fan-ziqi/My_HoloCubic/2.Firmware/HoloCubic-new/FirmwareCode/src/imu.h

#ifndef IMU_H
#define IMU_H


#include <I2Cdev.h>
#include <MPU6050.h>
#include "lv_port_indev.h"

#define IMU_I2C_SDA 32 
#define IMU_I2C_SCL 33


extern int32_t encoder_diff;
extern lv_indev_state_t encoder_state;
extern boolean image_flag;


enum ACTIVE_TYPE
{
      TURN_RIGHT = 0, TURN_LEFT, RETURN, GO_FORWORD, UNKNOWN
};

struct Imu_Active
{
	boolean  isValid;
	ACTIVE_TYPE active;
	boolean long_time;
	int16_t ax;
	int16_t ay;
	int16_t az;
	int16_t gx;
	int16_t gy;
	int16_t gz;
};

class IMU
{
private:
	MPU6050 imu;
	int flag;
	long  last_update_time;

	int16_t ax, ay, az;
	int16_t gx, gy, gz;

public:
	Imu_Active active_info;
	void init();
	Imu_Active* update(int interval);

};

#endif
