fan-ziqi/My_HoloCubic/2.Firmware/HoloCubic-new/FirmwareCode/src/lv_cubic_gui.c

/*********************
        INCLUDES
 *********************/
#include "lv_cubic_gui.h"
#include "images.h"

// 必须定义为全局或者静态
lv_obj_t *scr[4];

lv_obj_t *weather_image;
lv_obj_t *cityname_label;
lv_obj_t *temperature_label;
lv_obj_t *C_label;

lv_obj_t *time_image;
lv_obj_t *date_label;
lv_obj_t *time_label;

lv_obj_t *cpu_temp_label;
lv_obj_t *cpu_used_label;
lv_obj_t *mem_used_label;
lv_obj_t *net_upload_label;
lv_obj_t *net_download_label;

lv_obj_t *photo_image;

lv_font_declare(lv_font_montserrat_20);
lv_font_declare(lv_font_montserrat_24);
lv_font_declare(lv_font_montserrat_40);

// 天气图标路径的映射关系
void *image_map[] = {&Sunny, &Clear, "S:/Weather/2.bin", "S:/Weather/3.bin",
                     &Cloudy, &PartlyCloudy, &Overcast, &ModerateSnow,
                     &Thundershower, "S:/Weather/12.bin", &LightRain,
                     &ModerateRain, &HeavyRain, "S:/Weather/19.bin",
                     &Sleet, &SnowFlurry, &LightSnow, &HeavySnow,
                     "S:/Weather/26.bin", "S:/Weather/27.bin", "S:/Weather/28.bin",
                     "S:/Weather/29.bin", "S:/Weather/30.bin", "S:/Weather/31.bin",
                     "S:/Weather/32.bin", "S:/Weather/33.bin", "S:/Weather/34.bin",
                     "S:/Weather/35.bin", "S:/Weather/36.bin", "S:/Weather/37.bin",
                     "S:/Weather/38.bin", "S:/Weather/99.bin"};
int map_index[] = {0, 1, 2, 3, 4, 5, 5, 5, 5, 6,
                   7, 8, 9, 10, 11, 12, 12, 12, 12, 13,
                   14, 15, 16, 7, 17, 17, 18, 19, 20, 21,
                   22, 23, 24, 25, 26, 27, 28, 29, 30};

// static lv_group_t *g;
// static lv_obj_t *tv;
// static lv_obj_t *t1;
// static lv_obj_t *t2;
// static lv_obj_t *t3;
static lv_style_t default_style;
static lv_style_t label_style1;
static lv_style_t label_style3;
static lv_style_t label_style4;
static lv_style_t label_style5;

void display_init(void)
{
  lv_style_init(&default_style);
  lv_style_set_bg_color(&default_style, LV_STATE_DEFAULT, LV_COLOR_BLACK);
  lv_style_set_bg_color(&default_style, LV_STATE_PRESSED, LV_COLOR_GRAY);
  lv_style_set_bg_color(&default_style, LV_STATE_FOCUSED, LV_COLOR_BLACK);
  lv_style_set_bg_color(&default_style, LV_STATE_FOCUSED | LV_STATE_PRESSED, lv_color_hex(0xf88));
  lv_obj_add_style(lv_scr_act(), LV_BTN_PART_MAIN, &default_style);

  // scr[0] = lv_scr_act(); //在第一页创建
  // 天气页初始化
  scr[0] = lv_obj_create(NULL, NULL);
  lv_obj_add_style(scr[0], LV_BTN_PART_MAIN, &default_style);
  lv_style_init(&label_style1);
  lv_style_set_text_opa(&label_style1, LV_STATE_DEFAULT, LV_OPA_COVER);
  lv_style_set_text_color(&label_style1, LV_STATE_DEFAULT, LV_COLOR_WHITE);
  lv_style_set_text_font(&label_style1, LV_STATE_DEFAULT, &lv_font_montserrat_24);
  lv_style_init(&label_style3);
  lv_style_set_text_opa(&label_style3, LV_STATE_DEFAULT, LV_OPA_COVER);
  lv_style_set_text_color(&label_style3, LV_STATE_DEFAULT, LV_COLOR_WHITE);
  lv_style_set_text_font(&label_style3, LV_STATE_DEFAULT, &lv_font_montserrat_24);
  weather_image = lv_img_create(scr[0], NULL);
  cityname_label = lv_label_create(scr[0], NULL);
  temperature_label = lv_label_create(scr[0], NULL);
  C_label = lv_label_create(scr[0], NULL);

  // 日期时间页初始化
  scr[1] = lv_obj_create(NULL, NULL);
  lv_obj_add_style(scr[1], LV_BTN_PART_MAIN, &default_style);
  lv_style_init(&label_style5);
  lv_style_set_text_opa(&label_style5, LV_STATE_DEFAULT, LV_OPA_COVER);
  lv_style_set_text_color(&label_style5, LV_STATE_DEFAULT, LV_COLOR_WHITE);
  lv_style_set_text_font(&label_style5, LV_STATE_DEFAULT, &lv_font_montserrat_40);
  time_image = lv_img_create(scr[1], NULL);
  date_label = lv_label_create(scr[1], NULL);
  time_label = lv_label_create(scr[1], NULL);

  // 硬件信息页初始化
  scr[2] = lv_obj_create(NULL, NULL);
  lv_obj_add_style(scr[2], LV_BTN_PART_MAIN, &default_style);
  lv_style_init(&label_style4);
  lv_style_set_text_opa(&label_style4, LV_STATE_DEFAULT, LV_OPA_COVER);
  lv_style_set_text_color(&label_style4, LV_STATE_DEFAULT, LV_COLOR_WHITE);
  lv_style_set_text_font(&label_style4, LV_STATE_DEFAULT, &lv_font_montserrat_20);
  cpu_temp_label = lv_label_create(scr[2], NULL);
  cpu_used_label = lv_label_create(scr[2], NULL);
  mem_used_label = lv_label_create(scr[2], NULL);
  net_upload_label = lv_label_create(scr[2], NULL);
  net_download_label = lv_label_create(scr[2], NULL);

  scr[3] = lv_obj_create(NULL, NULL);
  photo_image = lv_img_create(scr[3], NULL);


}

void display_photo(const char *file_name)
{
  char buf[25] = {0};
  sprintf(buf, "S:/image/%s.bin", file_name);
  lv_img_set_src(photo_image, buf);
  lv_obj_align(photo_image, NULL, LV_ALIGN_CENTER, 0, 0);
}

void display_weather(const char *cityname, const char *temperature, int weathercode)
{
  void *path = image_map[map_index[weathercode]];
  if (weathercode < 39)
  {
    path = image_map[map_index[weathercode]];
  }
  else
  {
    path = image_map[31];
  }
  lv_img_set_src(weather_image, path);
  lv_obj_align(weather_image, NULL, LV_ALIGN_OUT_TOP_MID, 0, 150);

  lv_obj_add_style(cityname_label, LV_LABEL_PART_MAIN, &label_style1);
  lv_label_set_text(cityname_label, cityname);
  lv_obj_align(cityname_label, NULL, LV_ALIGN_OUT_BOTTOM_LEFT, 20, -60);

  lv_obj_add_style(temperature_label, LV_LABEL_PART_MAIN, &label_style3);
  lv_label_set_text(temperature_label, temperature);
  lv_obj_align(temperature_label, cityname_label, LV_ALIGN_OUT_RIGHT_MID, 10, 0);
  
  lv_obj_add_style(C_label, LV_LABEL_PART_MAIN, &label_style3);
  lv_label_set_text(C_label, "°C");
  lv_obj_align(C_label, temperature_label, LV_ALIGN_OUT_RIGHT_MID, 10, 0);
}

void display_time(const char *date, const char *time)
{
  // lv_img_set_src(time_image, &huoj);
  lv_img_set_src(time_image, &logo);
  lv_obj_align(time_image, NULL, LV_ALIGN_OUT_TOP_MID, 0, 120);

  lv_obj_add_style(date_label, LV_LABEL_PART_MAIN, &label_style5);
  lv_label_set_text(date_label, date);
  lv_obj_align(date_label, NULL, LV_ALIGN_OUT_BOTTOM_LEFT, 15, -100);

  lv_obj_add_style(time_label, LV_LABEL_PART_MAIN, &label_style5);
  lv_label_set_text(time_label, time);
  lv_obj_align(time_label, NULL, LV_ALIGN_OUT_BOTTOM_LEFT, 65, -50);
}

void display_hardware(const char *info)
{
  lv_obj_add_style(cpu_temp_label, LV_LABEL_PART_MAIN, &label_style4);
  lv_label_set_text_fmt(cpu_temp_label, "CPU Temp: %d °C", 0);
  lv_obj_set_pos(cpu_temp_label, 2, 30);

  lv_obj_add_style(cpu_used_label, LV_LABEL_PART_MAIN, &label_style4);
  lv_label_set_text_fmt(cpu_used_label, "CPU Used: %d\%", 0);
  lv_obj_set_pos(cpu_used_label, 2, 60);

  lv_obj_add_style(mem_used_label, LV_LABEL_PART_MAIN, &label_style4);
  lv_label_set_text_fmt(mem_used_label, "Mem Used: %dMB", 0);
  lv_obj_set_pos(mem_used_label, 2, 90);

  lv_obj_add_style(net_upload_label, LV_LABEL_PART_MAIN, &label_style4);
  lv_label_set_text_fmt(net_upload_label, "Net Upload: %dKB/s", 0);
  lv_obj_set_pos(net_upload_label, 2, 120);

  lv_obj_add_style(net_download_label, LV_LABEL_PART_MAIN, &label_style4);
  lv_label_set_text_fmt(net_download_label, "Net Download: %dKB/s", 0);
  lv_obj_set_pos(net_download_label, 2, 150);
}
